notefields7486/Emergency-Carbon-Respirator-Bottle-Edition/front2.jpg

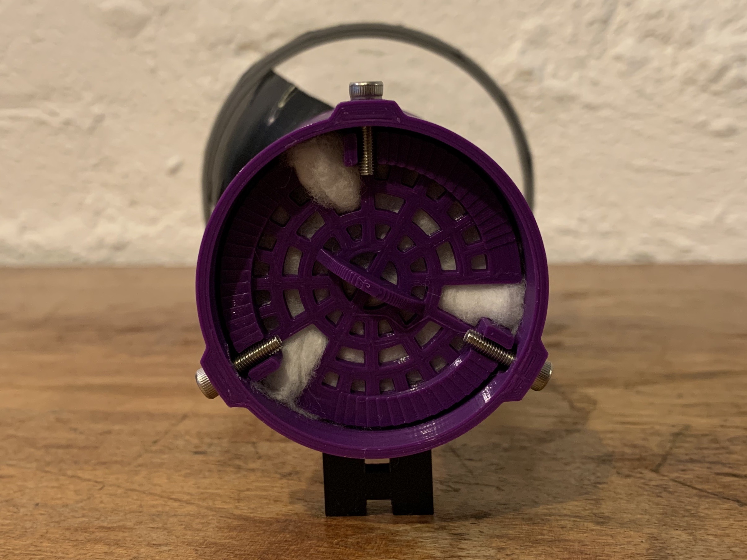
front2.jpg
